sjgray/Commodore-LCD-Remake/V1-Proto/3D/Case/STL/bottom-rev3.stl

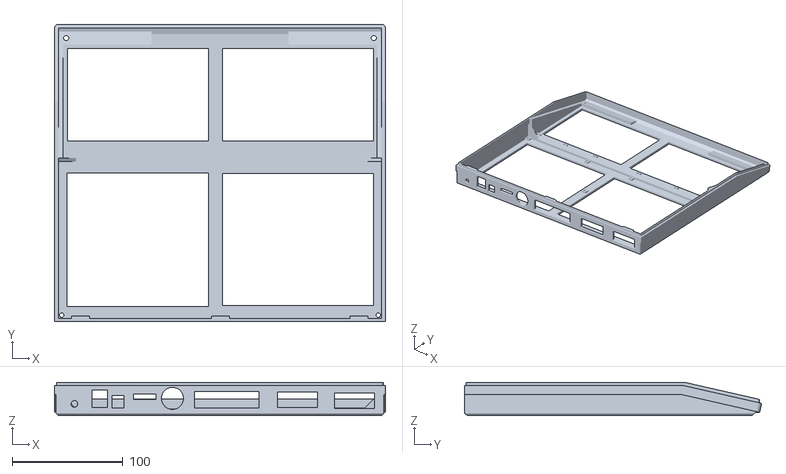
[picture p23: CAD file, 2025-12-20, an earlier design]
V1-Proto/3D/Case/STL/bottom-rev3.stl
299.0 x 268.7 x 30.0
