sjgray/Commodore-LCD-Remake/V1-Proto/3D/Case/STL/screen-front-rev8.stl

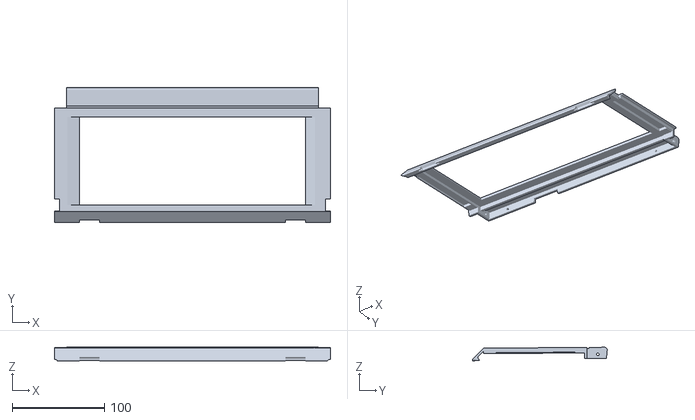
[picture p25: CAD file, 2025-12-20, an earlier design]
V1-Proto/3D/Case/STL/screen-front-rev8.stl
299.0 x 145.9 x 14.7
