sjgray/Commodore-LCD-Remake/V1-Proto/3D/Keycaps/clcd-1u-rev1.stl

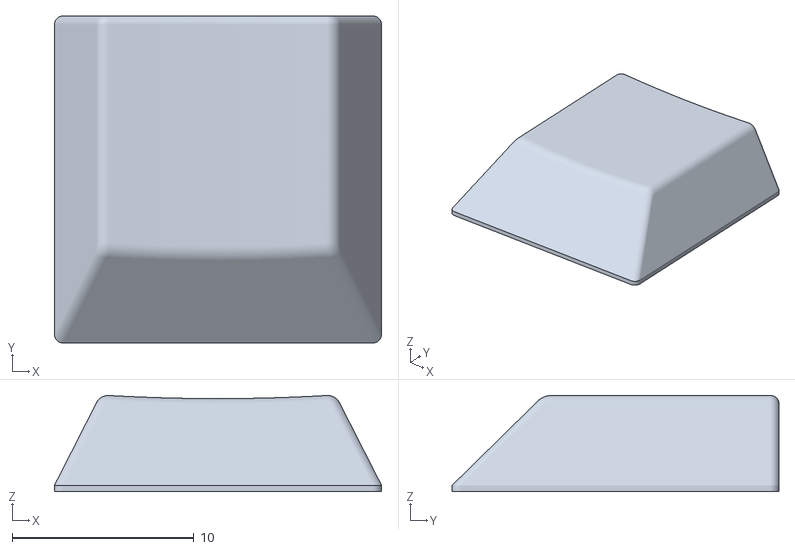
[picture p26: CAD file, 2025-12-20, an earlier design]
V1-Proto/3D/Keycaps/clcd-1u-rev1.stl
18.0 x 18.0 x 5.28
